Takazudo/zudo-pd/doc/SCAFFOLD.md

# Scaffold provenance

The initializer was run externally into `/tmp/pd-scaffold-S7V5WS/zudo-pd` on 2026-09-29:

```sh
pnpm create zudo-circuit-doc@0.1.0 <empty-scratch>/zudo-pd --name zudo-pd --title zudo-pd --library zudo-pd --agent both --yes --no-git --no-install
```

Each listed path was compared with that output. Exact copies: circuit templates, task examples,
checks README, package island seed and strict link checker. Root manifest/workspace, circuit
workflow/config, AGENTS entry, host manifest/config/routes/styles and ignore rules are merged
or derived; existing site identity, domain, GitHub, logo, CJK, sumi theme, history/body-foot
bindings and #206 header navigation are retained. Existing home route and tsconfig are retained
package-shaped equivalents. Canonical evidence skills were never overwritten.

| Path | Source | Full commit | Date | Track | Sync | Reason |
|---|---|---|---|---|---|---|
| `package.json` | `create-zudo-circuit-doc@0.1.0` output; Takazudo/zudo-circuit-doc scaffold | `5d0e2b630776489d394be341586b889dfe0d1cb8` | 2026-09-29 | releases | rerun pinned initializer externally, diff and merge | Project runtime adoption; preserve host and evidence rules |
| `pnpm-workspace.yaml` | `create-zudo-circuit-doc@0.1.0` output; Takazudo/zudo-circuit-doc scaffold | `5d0e2b630776489d394be341586b889dfe0d1cb8` | 2026-09-29 | releases | rerun pinned initializer externally, diff and merge | Project runtime adoption; preserve host and evidence rules |
| `circuit.config.ts` | `create-zudo-circuit-doc@0.1.0` output; Takazudo/zudo-circuit-doc scaffold | `5d0e2b630776489d394be341586b889dfe0d1cb8` | 2026-09-29 | releases | rerun pinned initializer externally, diff and merge | Project runtime adoption; preserve host and evidence rules |
| `AGENTS.md` | `create-zudo-circuit-doc@0.1.0` output; Takazudo/zudo-circuit-doc scaffold | `5d0e2b630776489d394be341586b889dfe0d1cb8` | 2026-09-29 | releases | rerun pinned initializer externally, diff and merge | Project runtime adoption; preserve host and evidence rules |
| `circuit/WORKFLOW.md` | `create-zudo-circuit-doc@0.1.0` output; Takazudo/zudo-circuit-doc scaffold | `5d0e2b630776489d394be341586b889dfe0d1cb8` | 2026-09-29 | releases | rerun pinned initializer externally, diff and merge | Project runtime adoption; preserve host and evidence rules |
| `circuit/agent-task-examples.md` | `create-zudo-circuit-doc@0.1.0` output; Takazudo/zudo-circuit-doc scaffold | `5d0e2b630776489d394be341586b889dfe0d1cb8` | 2026-09-29 | releases | rerun pinned initializer externally, diff and merge | Project runtime adoption; preserve host and evidence rules |
| `circuit/checks/README.md` | `create-zudo-circuit-doc@0.1.0` output; Takazudo/zudo-circuit-doc scaffold | `5d0e2b630776489d394be341586b889dfe0d1cb8` | 2026-09-29 | releases | rerun pinned initializer externally, diff and merge | Project runtime adoption; preserve host and evidence rules |
| `circuit/templates/**` | `create-zudo-circuit-doc@0.1.0` output; Takazudo/zudo-circuit-doc scaffold | `5d0e2b630776489d394be341586b889dfe0d1cb8` | 2026-09-29 | releases | rerun pinned initializer externally, diff and merge | Project runtime adoption; preserve host and evidence rules |
| `doc/package.json` | `create-zudo-circuit-doc@0.1.0` output; Takazudo/zudo-circuit-doc scaffold | `5d0e2b630776489d394be341586b889dfe0d1cb8` | 2026-09-29 | releases | rerun pinned initializer externally, diff and merge | Project runtime adoption; preserve host and evidence rules |
| `doc/zfb.config.ts` | `create-zudo-circuit-doc@0.1.0` output; Takazudo/zudo-circuit-doc scaffold | `5d0e2b630776489d394be341586b889dfe0d1cb8` | 2026-09-29 | releases | rerun pinned initializer externally, diff and merge | Project runtime adoption; preserve host and evidence rules |
| `doc/tsconfig.json` | `create-zudo-circuit-doc@0.1.0` output; Takazudo/zudo-circuit-doc scaffold | `5d0e2b630776489d394be341586b889dfe0d1cb8` | 2026-09-29 | releases | rerun pinned initializer externally, diff and merge | Project runtime adoption; preserve host and evidence rules |
| `doc/pages/index.tsx` | `create-zudo-circuit-doc@0.1.0` output; Takazudo/zudo-circuit-doc scaffold | `5d0e2b630776489d394be341586b889dfe0d1cb8` | 2026-09-29 | releases | rerun pinned initializer externally, diff and merge | Project runtime adoption; preserve host and evidence rules |
| `doc/pages/docs/[[...slug]].tsx` | `create-zudo-circuit-doc@0.1.0` output; Takazudo/zudo-circuit-doc scaffold | `5d0e2b630776489d394be341586b889dfe0d1cb8` | 2026-09-29 | releases | rerun pinned initializer externally, diff and merge | Project runtime adoption; preserve host and evidence rules |
| `doc/pages/lib/_circuit-doc-islands.ts` | `create-zudo-circuit-doc@0.1.0` output; Takazudo/zudo-circuit-doc scaffold | `5d0e2b630776489d394be341586b889dfe0d1cb8` | 2026-09-29 | releases | rerun pinned initializer externally, diff and merge | Project runtime adoption; preserve host and evidence rules |
| `doc/src/chrome-bindings.tsx` | `create-zudo-circuit-doc@0.1.0` output; Takazudo/zudo-circuit-doc scaffold | `5d0e2b630776489d394be341586b889dfe0d1cb8` | 2026-09-29 | releases | rerun pinned initializer externally, diff and merge | Project runtime adoption; preserve host and evidence rules |
| `doc/src/styles/global.css` | `create-zudo-circuit-doc@0.1.0` output; Takazudo/zudo-circuit-doc scaffold | `5d0e2b630776489d394be341586b889dfe0d1cb8` | 2026-09-29 | releases | rerun pinned initializer externally, diff and merge | Project runtime adoption; preserve host and evidence rules |
| `doc/scripts/check-links.js` | `create-zudo-circuit-doc@0.1.0` output; Takazudo/zudo-circuit-doc scaffold | `5d0e2b630776489d394be341586b889dfe0d1cb8` | 2026-09-29 | releases | rerun pinned initializer externally, diff and merge | Project runtime adoption; preserve host and evidence rules |
| `.gitignore` | `create-zudo-circuit-doc@0.1.0` output; Takazudo/zudo-circuit-doc scaffold | `5d0e2b630776489d394be341586b889dfe0d1cb8` | 2026-09-29 | releases | rerun pinned initializer externally, diff and merge | Project runtime adoption; preserve host and evidence rules |

Underlying create-zudo-doc 5.27.0 host scaffold source:
`zudolab/zudo-doc/packages/create-zudo-doc/templates/default/app`, full commit
`50cbd5c6c9e5a795d72a74a855e105e4939d4eab`. The package docs route retains the explicit
DocHistory binding and now imports the package island seed. Package MDX bindings and CSS
replace project evidence/preview UI; the unrelated task-list CSS workaround remains.

Intentional differences: raw agent resources remain disabled; header navigation is exactly
#206; asset indexing/listing stays off; sitemap is explicitly false because runtime 0.1.0
rejects nonempty sitemaps. TOC toggle, image enlargement and package asset viewer are enabled.
Source link warnings remain active and have a retained project log gate; strict rendered
HTML/anchor checks run in check:site. Public assets retain individual reviewed reasons and
all served paths. Historical PDF attachments do not establish fresh manufacturer verification.

The initializer README's stale “not on npm” paragraph ([upstream #102](https://github.com/Takazudo/zudo-circuit-doc/issues/102)) is deliberately omitted:
initializer/runtime 0.1.0 are published npm packages. Existing project README remains authoritative.
The root lock/workspace is authoritative; both consumers resolve patched runtime 0.1.0.
The global release-age bypass was removed; only observed too-fresh transitive hono@4.13.10
is explicitly excluded (published 2026-09-28T08:20:13Z).

Generated output is semantic parity, not byte identity: view model/report v2, default
zudo-circuit-doc marker, generated notice enabled, package descriptors and zcd classes replace
legacy zld markup. Existing evidence IDs/anchors and claim states remain authoritative.
Exact KiCad renderer digest/version/platform/layers/options remain unchanged; preview bytes
and model bytes remain unchanged. Project browser coverage stays separate: 12 representatives,
1440/375 widths, light/dark, missing-document c335982 and illustrative ASPI provenance. Three
explicit package representatives are supplementary.

Temporary runtime bridge: project #210 and [upstream reports #103–107](../patches/README.md). Keep the committed patch until
released behavior passes the retained compatibility regressions; upstream issue closure alone
is insufficient. No records, candidates, evidence fields or hardware checks were dropped.
The retired `doc/component-docs/` generator, callers and implementation tests are removed by
#208. The committed component pages and their stable history remain under
`doc/src/content/docs/components/`.

## Retained baseline origin

`circuit/tests/runtime-semantic-baseline.json` hashes every record's decoded identity,
aliases, sources, facts, coverage, interactions and pin maps, and all integration rules,
using recursively sorted object keys and preserved array order. It was captured read-only
from the legacy adapter at merged base `88c113ef9acd59e6c6fd6cee099686adf5e1d179` before
legacy retirement. Runtime tests compare the installed package projection to these hashes.
`runtime-anchor-baseline.json` captures every explicit EvidenceAnchor from all 64 committed
legacy pages at that same base. These baselines supplement #205's 313 covered project
file hashes and IDs; they do not assert generated MDX byte identity.

The bridge additionally rejects document exceptions naming nonexistent records, preserving
the old reference contract. The installed package regression is retained in references.test.ts.
At the initial #207 integration, legacy test/caller retirement remained for #208;
193 relocated project assertions, 14 compatibility regressions and the new runtime
contracts exercised the package. Cutover subsequently retained the remaining project
contracts and removed the legacy implementation.

## Asset-viewer publication boundary follow-up

The manager's guarded production build succeeded, but the subsequent real publication
scan rejected `dist/files/component-previews/footprints/manifest.json/index.html`: generic
asset-viewer HTML mirrored a package preview manifest and exposed a denied evidence
`[29].sources[2].sha256` value. The reviewed package manifest hash allowance applies only
to the package-owned artifact; it must not excuse another generated HTML projection.

The host now uses `assetViewerExclude: ["component-previews/**"]`, relative to the
installed zudo-doc 5.27.0 asset directory `public/assets` (verified in its `scanAssets`
and routes-plugin implementation). It excludes footprint SVGs, WRL models and manifests
from generic viewer route generation while retaining their existing public URLs and
package reference cards/inline dialogs. Generic manually authored asset viewing stays
enabled. Asset viewer listing and all indexing are explicitly false. No public assets,
canonical evidence, package patch or scanner/hash checks were changed. A retained
installed-snapshot regression proves an unexcluded manifest becomes viewer HTML, then
proves the host exclusion removes that mirror while a manual asset still renders.

## Browser launcher and heading-extractor bridges

Manager-controlled browser evidence: the unmodified runtime launcher failed the unchanged
idle assertion (`20` → `22`, 45 seconds); the same CLI/site/assertions/timeouts passed all
24 package responsive/theme cases and complete interaction/idle/SPA/fallback/no-JS checks
when a CHROME_BIN wrapper added only the three baseline foreground flags (27 seconds,
minimum memory 6692 MB). The runtime bridge now restores those three flags and the
baseline `Page.bringToFront` lifecycle. Product rendering, idle assertions and timeouts
are unchanged. Upstream: https://github.com/Takazudo/zudo-circuit-doc/issues/108;
removal remains https://github.com/Takazudo/zudo-pd/issues/210. A fake executable/CDP
regression executes the installed launcher and verifies received argv, foreground command
order, normal child/profile cleanup and cleanup on connection failure; it runs no browser.

A separate `@takazudo/zudo-doc@5.27.0` pnpm patch changes only shipped synchronous
`dist/extract-headings/index.js`. Upstream: https://github.com/zudolab/zudo-doc/issues/4428;
independent removal tracker: https://github.com/Takazudo/zudo-pd/issues/211. The strict
scaffold gate found 30 false source-anchor misses after one-line triple-backtick spans in
archived circuit-diagrams, plus four real dead built TOC links where `&gt;1000ms`/`&lt;2mm`
were slugged as literal entity names. The bridge correctly distinguishes inline spans
from true fences and decodes complete Markdown character references exactly once outside
protected escaped/code spans, using the package's declared parse5 full named-entity
parser. Markdown rejects unknown partial names and replaces invalid control/scalar numeric
references; native-pipeline regressions protect those differences from HTML parsing.

`circuit/tests/heading-built-baseline.json` captures all 101 h2–h6 IDs from the manager's
production-built circuit-diagrams, ch224d and linear-regulator-capacitors pages. Additional
fixtures compare installed SDK helpers directly to the pinned zfb 2.21.0 native Markdown
pipeline compiled to WASM, using hierarchical IDs. They cover full named/numeric entities,
escaped/code literals, Unicode arrows/non-Latin, duplicate nesting, h5/h6, true and invalid
fence closers, inline triple spans and indented code. No archived source bytes, evidence,
header navigation, anchor allowlist, strict-check threshold or scanner exceptions changed.

## Long package identity layout bridge

The full 12-representative browser contract found a real c3024223 containment defect at
375px/light: viewer/caption/viewport left 41, right 356.359, width 315.359 exceeded the
reference card's right edge 336 (card width 312). Package label
`SMA_Diodes_SDT5A60SA_C3024223` expanded the viewer's implicit auto-minimum grid track.
Manager-controlled live CSS, with no DOM/text/assertion changes, made all three right edges
319 and widths 278 while preserving the exact label bytes (guard PASS, four seconds,
minimum memory 7507 MB). The proven rule set is now patched into package-owned styles.css:
explicit minmax(0,1fr) viewer column, zero viewer/direct-item minima, caption wrapping and
viewport border-box sizing. No label truncation/clipping and no browser threshold changes.
Upstream: https://github.com/Takazudo/zudo-circuit-doc/issues/109; removal tracker #210.
Long-identity descriptor/SSR/accessible-label and CSS sizing regressions are retained;
the manager reruns all 48 project width/theme cases as the actual geometry proof.
CSS guidance applied: `flexbox-and-grid/grid-patterns.mdx` and
`text-control/long-url-and-path-wrapping.mdx` from zudo-css-wisdom. Identity remains plain
copyable text; no new renderer or host-specific preview stylesheet was introduced.

## Named footprint modal accessibility contract (supersedes the alt bridge)

The earlier migration directive interpreted the project prefix-only enlarged-image alt
assertion as an SDK defect and temporarily restored nonempty image alt under #110.
The combined manager gate then proved that conflicts with the intentional SDK contract:
the media-only modal carries the full accessible description through `aria-label`, while
its enlarged image is decorative (`alt=""`) to avoid a duplicate description. That
inappropriate bridge is removed; the shipped footprint island and first-line client
directive are restored unchanged. #110 is an intentional-design correction, not a runtime
#210 removal prerequisite.

The separate project browser contract now checks the complete semantic identity rather
than the old prefix: inline image alt exactly equals `Footprint preview for <full package
name>`; modal aria-label exactly equals that inline description; enlarged image alt is
empty; no aria-labelledby points at the removed visible title. All other modal, focus,
media containment, load/error, gesture, no-JS, idle assertions and timings are retained.
The installed-island regression exercises the actual trigger, real dialog SSR markup,
exact identity, decorative image and meaningful error fallback with only hooks/modal
effects controlled, without launching a browser. This is the documented package UI
adaptation; no component identity is hidden or truncated. Correction tracking:
https://github.com/Takazudo/zudo-circuit-doc/issues/110.

## Root host lifecycle context

Root build, dev and host checks enter `doc/` through
`circuit/scripts/doc-command.sh`. The wrapper clears the inherited root pnpm
`INIT_CWD` before starting the doc lifecycle, so the history CLI resolves
`src/content/docs` in the actual host. Root PR CI exposed the old context as an
invalid workspace-root history candidate; the strict warning gate remains
unchanged. Explicit local `GEN_DOC_HISTORY=1` verification covers the CI history
path as well as ordinary builds.

Cutover deliberately updates the hash for the live workflow guide
`.claude/skills/component-spec-audit/references/new-component-workflow.md` from
`d47eee9d71c50b15756b1e39236c613027d6ccf285a4aefcd69aa900efbb92b0` to
`73cdc1e7f34e0a3fc72d7260626354b7e2aa74a6c548a521daf4e7a1fd757891`.
The reviewed change describes the actual A/B/P provider and root commands; the
other 312 covered files, canonical evidence, validators and hardware inputs
remain unchanged.

## PR preview first deployment

The PR preview uses the top-level `zudo-pd` Worker; production uses the separate
`production` environment and custom-domain route. Version upload requires an
existing Worker. The CI-only preview helper propagates pipeline failures,
bootstraps the top-level Worker only on Wrangler's specific missing-Worker
error, and requires a returned alias URL before the route smoke can run.
Authentication, bootstrap and retry failures remain failures. All preview calls
explicitly use the empty top-level environment; production commands are unchanged.

References: [Wrangler environments](https://developers.cloudflare.com/workers/wrangler/environments/)
and [aliased version URLs](https://developers.cloudflare.com/workers/versions-and-deployments/version-urls/).
