Takazudo/zudo-pd/notes/diagram.md

## Diagram1: USB-PD給電部

```
USB-C コネクタ                    CH224Q (DFN-10-EP)                LED状態表示回路
┌─────────────┐                ┌──────────────┐                 ┌─────────────┐
│VBUS (B9,A9) ├──┬─────────────┤1. VHV        │                 │   VDD 3.3V  │
│             │  │             │8. VBUS       │─┬─→ 15V出力     │      │      │
│CC1 (A5)     ├──┼─────────────┤7. CC1        │ │               │    330Ω     │
│CC2 (B5)     ├──┼─────────────┤6. CC2        │ │               │   (R1)      │
│GND (B12,A12)├──┼─────────────┤GND           │ │               │      │      │
└─────────────┘  │             │11. EP        │←┘               │   赤色LED   │
                 │             │              │                 │   (LED1)    │
               ┌─C1            │9. CFG1       │←── GND          │      │      │
               │ 10µF/25V      │2. CFG2/SCL   │←── Open         │  PG ────────┘
               │               │3. CFG3/SDA   │←── Open         │              
               └─┬───          │10. PG        │─────────────────┘              
                 │             │4. DP         │    (接続なし)                   
               ┌─C2            │5. DM         │    (接続なし)                   
               │ 10µF/25V      └──────────────┘                                 
               │                      │                                        
               └─┬────────────────────┘                                        
                 │                                                             
                GND
```

## Diagram2: USB-PD給電部 +15V → +13.5V 降圧回路 (LM2596S-ADJ #1)

```
+15V ─────┬─── L1: 100µH ──┬─── D1 ──┬─── C3: 470µF/25V ──┬─→ +13.5V/1.3A
          │    (4.5A)      │   SS34  │    (入力フィルタ)   │
          │                │    ↓    │                    │
          │           ┌────┴─────────┴──┐                 │
          │           │5  VIN      VOUT │4────────────────┤
          └───────────┤3  ON        FB  │2────────┬───────┘
                      │1  GND           │         │
                      └─────────────────┘         │
                              │                   │
                             GND              ┌────┴───┐
                                              │ R1     │ 10kΩ (実際13.53V)
                                              │ 10kΩ   │
                                              └────┬───┘
                                              ┌────┴───┐
                                              │ R2     │ 1kΩ
                                              │ 1kΩ    │
                                              └────┬───┘
                                                   │
                                                  GND
```

## Diagram3: +15V → +7.5V 降圧回路 (LM2596S-ADJ #2)

```
+15V ─────┬─── L2: 100µH ──┬─── D2 ──┬─── C4: 470µF/10V ──┬─→ +7.5V/0.6A
          │    (4.5A)      │   SS34  │    (入力フィルタ)   │
          │                │    ↓    │                    │
          │           ┌────┴─────────┴──┐                 │
          │           │5  VIN      VOUT │4────────────────┤
          └───────────┤3  ON        FB  │2────────┬───────┘
                      │1  GND           │         │
                      └─────────────────┘         │
                              │                   │
                             GND              ┌────┴───┐
                                              │ R3     │ 5.1kΩ (実際7.50V)
                                              │ 5.1kΩ  │
                                              └────┬───┘
                                              ┌────┴───┐
                                              │ R4     │ 1kΩ
                                              │ 1kΩ    │
                                              └────┬───┘
                                                   │
                                                  GND
```

## Diagram4: +15V → -15V 電圧反転回路 (ICL7660)

```
+15V ─────┬─────────────────────────────────────────┬─→ +15V (他回路へ)
          │                                         │
          │           ICL7660M/TR                   │
          │         ┌──────────────┐                │
          └─────────┤2,8  V+   CAP+│1──┐            │
                    │              │   │            │
           GND ─────┤3   GND   CAP-│4──┼─┐          │
                    │              │   │ │          │
          OPEN ─────┤6   LV    V-  │5──┼─┼──────────┴─→ -15V
                    │              │   │ │
          OPEN ─────┤7   OSC       │   │ │
                    └──────────────┘   │ │
                                       │ │
                     C9: 10µF セラミック │ │
                    ┌───────────────────┘ │
                    │                     │
                    └─────────────────────┘
                    
                    C10: 10µF セラミック
                    ┌─────────────────────────┐
                    │                         │
            -15V ───┼─────────────────────────┼─── GND
                    │                         │
                    └─────────────────────────┘
```

**フライングキャパシタ（C9）はPIN1とPIN4の間に直接接続**

```
      フライングキャパシタ C9 (10µF)
           ┌─────────┐
PIN1 ──────┤+       -├────── PIN4
(CAP+)     └─────────┘     (CAP-)
```

## Diagram5: -15V → -13.5V 降圧回路 (LM2596S-ADJ #3)

```
-15V ─────┬─── L3: 100µH ──┬─── D3 ──┬─── C7: 470µF/25V ──┬─→ -13.5V/0.9A
          │    (4.5A)      │   SS34  │    (入力フィルタ)   │
          │                │    ↓    │                    │
          │           ┌────┴─────────┴──┐                 │
          │           │5  VIN      VOUT │4────────────────┤
          └───────────┤3  ON        FB  │2────────┬───────┘
                      │1  GND           │         │
                      └─────────────────┘         │
                              │                   │
                             GND              ┌────┴───┐
                                              │ R5     │ 10kΩ (実際-13.53V)
                                              │ 10kΩ   │
                                              └────┬───┘
                                              ┌────┴───┐
                                              │ R6     │ 1kΩ
                                              │ 1kΩ    │
                                              └────┬───┘
                                                   │
                                                  GND
```

## Diagram6: +13.5V → +12V リニアレギュレータ

```
+13.5V ──┬─── C11: 470nF ───┬─── LM7812 ───┬─── C14: 100nF ───┬─→ +12V/1.2A
         │                  │   (TO-220)   │                  │
         │                  │    ┌─────┐   │                  │
         │                  └────│1 IN │3──┴──────────────────┤
         │                       │     │                      │
         │                    ┌──│2 GND│                      │
         │                    │  └─────┘                      │
         │                    │     │                         │
         └─── C17: 470µF ─────┼─────┼─── C18: 470µF ──────────┤
              (入力安定化)     │     │    (出力安定化)         │
                               │     │                         │
                              GND   GND                       │
                                                              │
                     ┌────────────────────────────────────────┘
                     │
               ┌─────┴─────┐  1kΩ (R7)
               │    LED2   │ ──────┬─→ +12V状態表示 (緑LED)
               │  (緑色)   │       │
               └─────┬─────┘       │
                     │            GND
                    GND
```

## Diagram7: +7.5V → +5V リニアレギュレータ

```
+7.5V ───┬─── C12: 470nF ───┬─── LM7805 ───┬─── C15: 100nF ───┬─→ +5V/1.2A
         │                  │  (TO-220F-3) │                  │
         │                  │    ┌─────┐   │                  │
         │                  └────│1 IN │3──┴──────────────────┤
         │                       │     │                      │
         │                    ┌──│2 GND│                      │
         │                    │  └─────┘                      │
         │                    │     │                         │
         └─── C19: 470µF ─────┼─────┼─── C20: 470µF ──────────┤
              (入力安定化)     │     │    (出力安定化)         │
                               │     │                         │
                              GND   GND                       │
                                                              │
                     ┌────────────────────────────────────────┘
                     │
               ┌─────┴─────┐  1kΩ (R8)
               │    LED3   │ ──────┬─→ +5V状態表示 (青LED)
               │  (青色)   │       │
               └─────┬─────┘       │
                     │            GND
                    GND
```

## Diagram8: -13.5V → -12V リニアレギュレータ

```
-13.5V ──┬─── C13: 470nF ───┬─── LM7912 ───┬─── C16: 100nF ───┬─→ -12V/1.0A
         │                  │   (TO-220)   │                  │
         │                  │    ┌─────┐   │                  │
         │                  └────│1 IN │2──┴──────────────────┤
         │                       │     │                      │
         │                    ┌──│3 GND│                      │
         │                    │  └─────┘                      │
         │                    │     │                         │
         └─── C21: 470µF ─────┼─────┼─── C22: 470µF ──────────┤
              (入力安定化)     │     │    (出力安定化)         │
                               │     │                         │
                              GND   GND                       │
                                                              │
                     ┌────────────────────────────────────────┘
                     │
               ┌─────┴─────┐  1kΩ (R9)
               │    LED4   │ ──────┬─→ -12V状態表示 (赤LED)
               │  (赤色)   │       │
               └─────┬─────┘       │
                     │            GND
                    GND
```

## Diagram9: 保護回路（初心者対応・2段階保護）

```
+12V ──┬─── PTC1: 1.1A ──┬─── F1: 2A ───┬─── TVS1: SMAJ15A ───┬─→ +12V OUT
       │   (自動復帰)     │  (バックアップ)│    (15V一方向)      │
       │                 │              │      ↓              │
       │                 │              └─────GND─────────────┤
       │                 │                                    │
       │                 └─── LED2: 緑 ──[R7: 1kΩ]──┬─→ 電源状態表示
       │                                             │
       │                                            GND
       │
       └─── 段階的保護:
            1. 過負荷 (1.2-2A) → PTC遮断 → 30秒後自動復帰 ✅
            2. 短絡 (>2A) → ヒューズ溶断 → 修理必要 ❌

+5V ───┬─── PTC2: 0.75A ─┬─── F2: 1.5A ──┬─── TVS2: PRTR5V0U2X ─┬─→ +5V OUT
       │   (自動復帰)     │  (バックアップ)│    (5V双方向)        │
       │                 │              │      ↕               │
       │                 │              └─────GND──────────────┤
       │                 │                                    │
       │                 └─── LED3: 青 ──[R8: 1kΩ]──┬─→ 電源状態表示
       │                                             │
       │                                            GND
       │
       └─── 段階的保護 (同上)

-12V ──┬─── PTC3: 0.9A ──┬─── F3: 1.5A ──┬─── TVS3: SMAJ15A ───┬─→ -12V OUT
       │   (自動復帰)     │  (バックアップ)│   (15V一方向逆接続)  │
       │                 │              │      ↑              │
       │                 │              └─────GND─────────────┤
       │                 │                                    │
       │                 └─── LED4: 赤 ──[R9: 1kΩ]──┬─→ 電源状態表示
       │                                             │
       │                                            GND
       │
       └─── 段階的保護 (同上)

※ TVS3は負電圧保護のため、カソードを-12Vライン、アノードをGNDに接続
※ PTCは通常時ほぼ抵抗ゼロ、過電流時に高抵抗化して電流を制限
※ ヒューズはPTCが対応できない急激な短絡から保護
※ LEDが消えたら過負荷 → モジュールを減らして30秒待つ
```

## Diagram10: 電源フロー概要

```
USB-C 15V ──┬─→ +13.5V (DC-DC) ──→ +12V (LDO) ──→ +12V OUT
            │
            ├─→ +7.5V  (DC-DC) ──→ +5V  (LDO) ──→ +5V OUT
            │
            └─→ -15V (反転) ──→ -13.5V (DC-DC) ──→ -12V (LDO) ──→ -12V OUT
```
