Takazudo/zudo-pd/3dp-files/adhesive-leg/generated/four-up.png

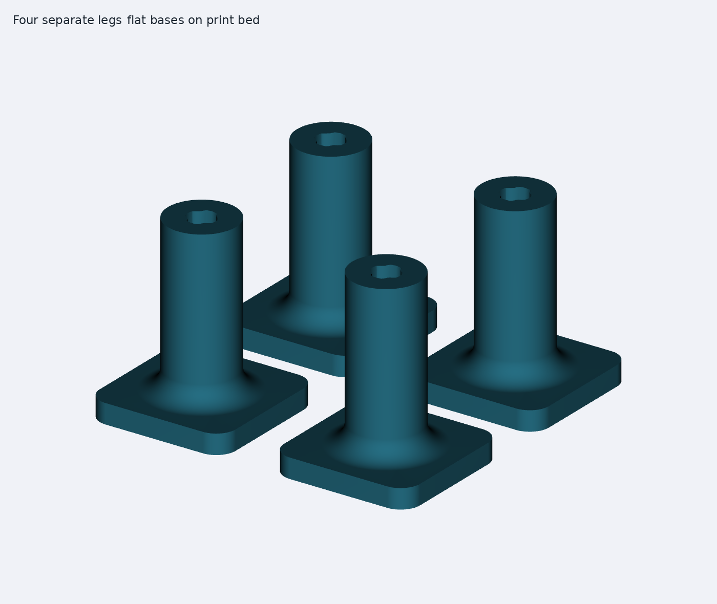
3dp-files/adhesive-leg/generated/four-up.png
