Takazudo/zudo-pd/3dp-files/adhesive-leg/generated/preview.png

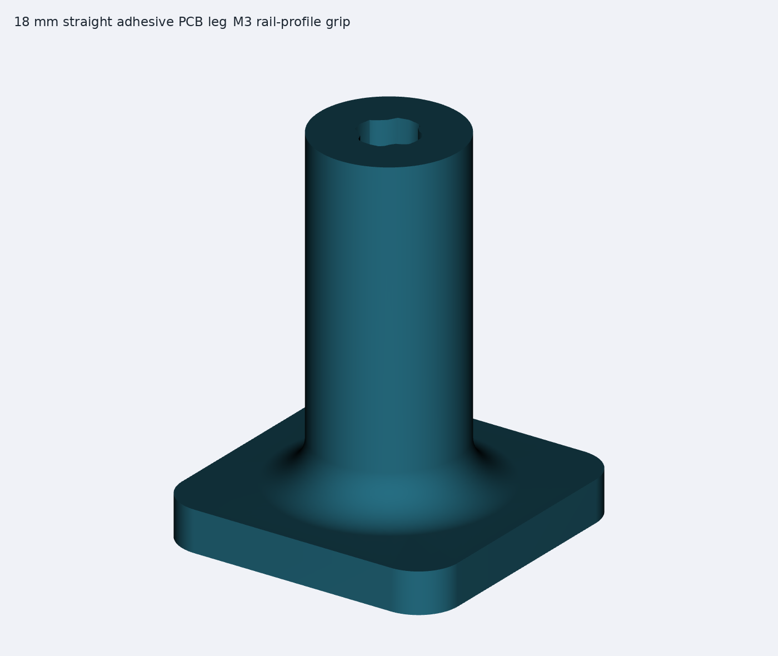
3dp-files/adhesive-leg/generated/preview.png
