Takazudo/zudo-pd/3dp-files/adhesive-leg/generated/section.png

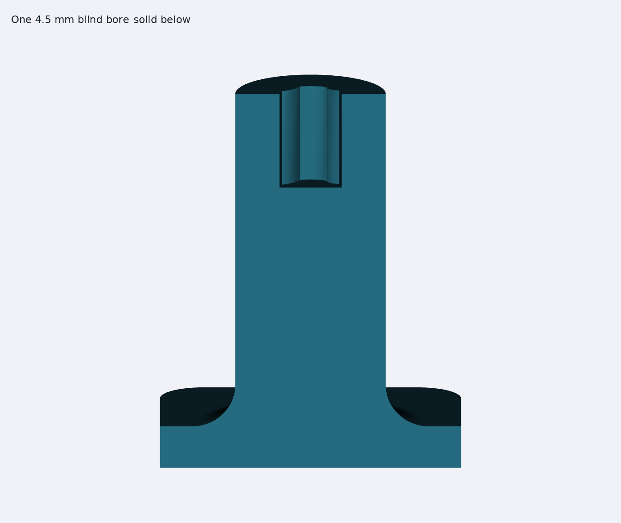
3dp-files/adhesive-leg/generated/section.png
