Takazudo/zudo-pd/boards/board-b/artwork/back-portrait-preview.png

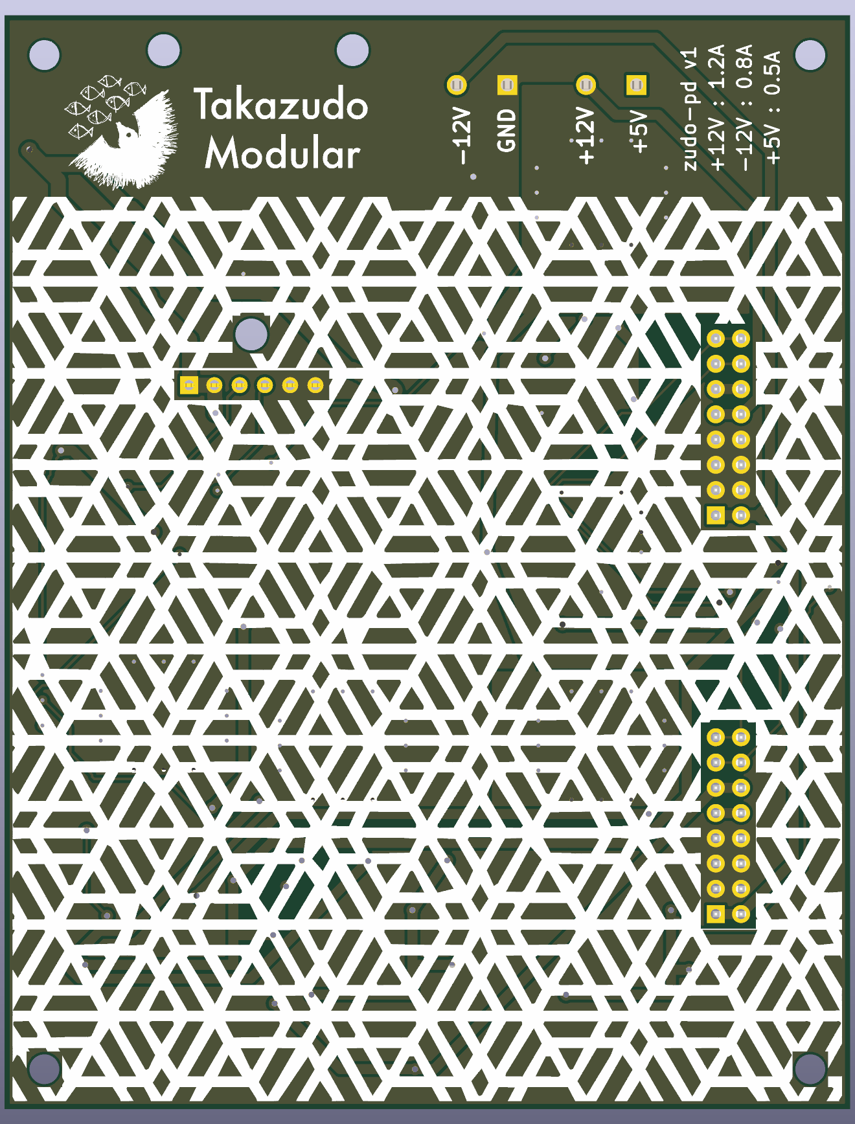
boards/board-b/artwork/back-portrait-preview.png
