Takazudo/zudo-pd/boards/board-b/artwork/back-preview.png

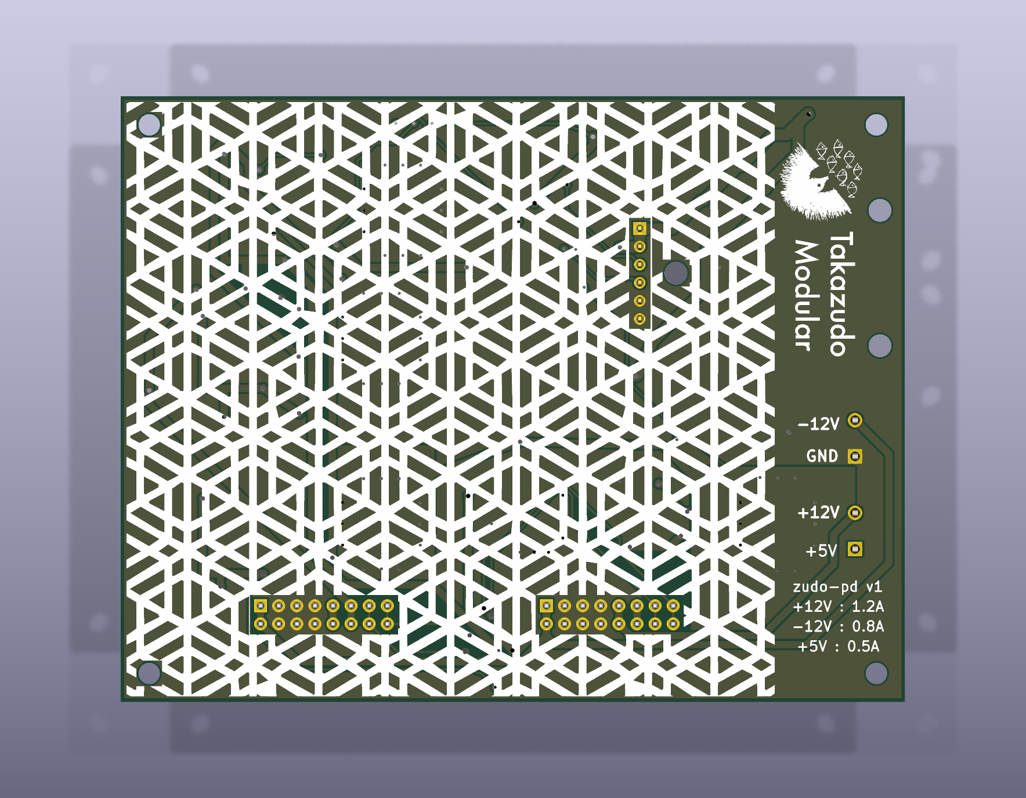
boards/board-b/artwork/back-preview.png
