Takazudo/zudo-pd/doc/src/content/docs/components/l7812cv.md

---
title: L7812CD2T-TR - +12V Linear Regulator
sidebar_position: 9
---

Fixed positive voltage regulator providing stable +12V output in compact TO-263-2 (D2PAK) surface-mount package with excellent thermal performance.

- [View on JLCPCB: C13456](https://jlcpcb.com/partdetail/C13456)
- [Download Datasheet (PDF)](/datasheets/L7812CD2T-datasheet.pdf)

L7812CD2T TO-263-2 Package

## Overview

The L7812CD2T-TR is a three-terminal positive voltage regulator in TO-263-2 (D2PAK) package, designed to provide a fixed +12V output from a higher input voltage. This component serves as the final stage in the +12V power rail, converting the +13.5V DC-DC output to a clean, low-noise +12V suitable for modular synthesizer applications.

## Key Specifications

| Parameter | Value | Notes |
| --- | --- | --- |
| **JLCPCB Part Number** | C13456 | |
| **Manufacturer Part Number** | L7812CD2T-TR | |
| **Package** | TO-263-2 (D2PAK) | Surface-mount |
| **Stock Availability** | 40,204 units | Very high availability |
| **Unit Price** | $0.11 | JLCPCB pricing |
| **Output Voltage** | 12V ±4% | 11.52V - 12.48V |
| **Output Current** | 1.5A max | Design uses 1.2A |
| **Dropout Voltage** | ~2V typical | Minimum VIN = 14V |
| **Line Regulation** | ±0.5% typical | Input voltage variation  |
| **Load Regulation** | ±1% typical | Output current variation |
| **Ripple Rejection** | &gt;60dB | @120Hz |
| **Quiescent Current** | ~5mA typical | No-load consumption |
| **Thermal Resistance θJC** | 3°C/W | Junction to case (tab) |
| **Thermal Resistance θJA** | 35°C/W | Junction to ambient |
| **Operating Temp Range** | 0°C to +125°C | Junction temperature |

## Pin Configuration

```
         TO-263-2 (D2PAK) Package
              Top View

         ┌──────────────┐
         │              │
         │   L7812C     │
         │   D2T-TR     │
         │              │
         │              │
         └──┬───────┬───┘
            │       │
          PIN1    PIN2
          INPUT    GND
         (+13.5V) (Common)

              TAB
           (OUTPUT)
            (+12V)

         Side View

         ┌──────────────┐
         │   Component  │ ← Surface mount IC
         └──┬───────┬───┘
            │       │
          PIN1    PIN2

    ════════════════════  ← Metal tab (OUTPUT)
                            soldered to PCB pad
```

### Pin Descriptions

| Pin | Name | Function | Connection in Design |
| --- | --- | --- | --- |
| 1 | INPUT  | Unregulated input voltage | +13.5V from DC-DC converter (U2)  |
| 2 | GND | Ground reference (common) | System ground plane |
| TAB | OUTPUT | Regulated +12V output (metal tab) | +12V rail with protection circuit |

**Note**: Unlike TO-220 package, the TO-263-2 has the OUTPUT on the metal tab, not on pin 3.

## Application Circuit

```
+13.5V (from DC-DC) ───┬─── C11: 470nF ───┬─── U6: L7812CD2T ───┬─── C14: 100nF ───┬─→ +12V OUT
                       │                  │                      │                  │
                       │                  │    ┌──────────┐      │                  │
                       │                  └────│1  INPUT  │      │                  │
                       │                       │          │      │                  │
                       │                    ┌──│2   GND   │      │                  │
                       │                    │  │          │      │                  │
                       │                    │  │   TAB ───┴──────┴──────────────────┤
                       │                    │  └──────────┘                         │
                       │                    │     (OUTPUT)                          │
                       └─── C17: 470µF ─────┼─────────┬─── C18: 470µF ──────────────┤
                            (Input)         │         │    (Output)                 │
                                            │         │                             │
                                           GND       GND                            │
                                                                                    │
                                        ┌───────────────────────────────────────────┘
                                        │
                                  ┌─────┴─────┐
                                  │   LED2    │ Green Status LED
                                  │  (Green)  │ via R7: 1kΩ
                                  └─────┬─────┘
                                        │
                                       GND
```

## Component Values

### Input Capacitors

| Reference | Value | Type | Voltage | Package | Part Number | Purpose |
| --- | ----- | --- | --- | --- | --- | --- |
| C11 | 470nF | Ceramic X7R  | 25V | 0603 | C1623 | High-frequency noise filtering |
| C17 | 470µF | Electrolytic | 10V | D6.3xL7.7mm | C335982 | Input voltage stabilization |

### Output Capacitors

| Reference | Value | Type | Voltage | Package | Part Number | Purpose |
| --- | ----- | --- | --- | --- | --- | --- |
| C14 | 100nF | Ceramic X7R  | 50V | 0805 | C1711 | High-frequency decoupling |
| C18 | 470µF | Electrolytic | 10V | D6.3xL7.7mm | C335982 | Load transient response |

### Status LED Circuit

| Reference | Part | Value | Package | Part Number | Purpose |
| --- | --- | --- | --- | --- | --- |
| LED2 | Green LED | 2.0V @ 10mA | 0805 | C72043 | Power status indicator |
| R7 | Resistor  | 1kΩ | 0603 | C21190 | LED current limiting |

## Design Considerations

### Input Voltage Requirements

The L7812CV requires a minimum input voltage of approximately 14V for proper regulation (12V output + 2V dropout). In this design:

- **Input voltage**: +13.5V from LM2596S DC-DC converter
- **Dropout margin**: 13.5V - 12V = 1.5V
- **Status**: ⚠️ Marginal - operates near minimum dropout voltage

The 1.5V margin is slightly below the typical 2V dropout specification but acceptable because:

1. The DC-DC stage is regulated at 13.5V (not 13.53V as calculated from feedback)
2. The L7812CV can regulate with 1.5V dropout at lower currents
3. Actual load current (1.2A) is below maximum rating (1.5A)

**Recommendation**: For production, consider increasing DC-DC output to 14.0V for better dropout margin.

### Thermal Management

Power dissipation calculation:

```
P = (VIN - VOUT) × IOUT
P = (13.5V - 12V) × 1.2A
P = 1.5V × 1.2A
P = 1.8W
```

Temperature rise without additional heatsinking:

```
ΔT = P × θJA
ΔT = 1.8W × 35°C/W
ΔT = 63°C
```

At 25°C ambient, junction temperature = 88°C (well within 125°C maximum).

**Thermal performance advantages of TO-263-2**:

- Lower θJA than TO-220 (35°C/W vs 50°C/W)
- Large metal tab provides excellent heat spreading
- Direct thermal contact with PCB copper pour
- No additional heatsink required for this application

**PCB copper area recommendations**:

- Minimum: 3 cm² copper pour connected to tab
- Recommended: 6 cm² copper pour for better margin
- Thermal vias: 6-10 vias (0.3mm) under tab to bottom layer

### Capacitor Placement

Critical for stability and noise rejection:

1. **C11 (470nF ceramic)**: Place within 5mm of pin 1

- Purpose: Suppress high-frequency noise from DC-DC stage
- Type: X7R or better (C0G ideal but more expensive)

2. **C17 (470µF electrolytic)**: Place within 10mm of pin 1

- Purpose: Stabilize input voltage during load transients
- Polarity: Positive terminal to input, negative to ground

3. **C14 (100nF ceramic)**: Place within 5mm of output tab

- Purpose: High-frequency output decoupling
- Critical for preventing oscillation
- Must be ceramic for low ESR/ESL

4. **C18 (470µF electrolytic)**: Place within 10mm of output tab

- Purpose: Improve load transient response
- ESR: &lt;2Ω for best performance
- Helps with sudden current demands

### Ground Plane Connection

The TO-263-2 package requires careful PCB layout:

- **Pin 2 (GND)**: Connect directly to ground plane with wide trace
- **Tab (OUTPUT)**: Large copper pour for both electrical and thermal connection
- **Thermal vias**: Essential for heat dissipation to inner/bottom layers
- **Keep-out area**: Maintain clearance around pins for solder inspection

## Performance Characteristics

### Regulation Performance

| Condition | Specification | Typical Performance |
| --- | --- | --- |
| Line regulation | VIN = 14.5V to 27V | ±0.5% (±60mV) |
| Load regulation | IOUT = 5mA to 1.5A | ±1% (±120mV) |
| Output voltage accuracy | At 25°C | ±4% (±480mV) |
| Temperature coefficient | -40°C to +125°C | ±1mV/°C typical |

### Noise Performance

| Parameter | Value | Conditions |
| --- | --- | --- |
| Ripple rejection | 60dB min | f = 120Hz |
| Output noise voltage | &lt;1mVp-p | With recommended capacitors |
| Transient response | &lt;50µs | 500mA load step |

## Protection Features

### Built-in Protections

1. **Thermal Shutdown**: Automatically shuts down if junction temperature exceeds 150°C
2. **Short Circuit Protection**: Current limiting prevents damage during output short
3. **Safe Operating Area (SOA)**: Internal circuitry ensures operation within safe limits

### External Protection (This Design)

```
+12V (from U6) ──┬─── PTC1: 1.1A ──┬─── F1: 2A ───┬─── TVS1: SMAJ15A ───┬─→ +12V OUT
                 │  (Auto-Reset)   │   (Backup)   │   (15V Clamp)       │
                 │                 │              │      ↓              │
                 │                 │              └─────GND─────────────┤
                 │                 │                                    │
                 └─── LED2 (Green) via R7 (1kΩ) ──────────────→ Power Status
```

Protection stages:

1. **Overload (1.2A-2A)**: PTC1 trips → Auto-reset after cooling
2. **Short circuit (&gt;2A)**: F1 blows → Manual replacement required
3. **Overvoltage**: TVS1 clamps transients above 15V

## Bill of Materials

| Designator | Part | Value | Package | JLCPCB Part # | Qty | Unit Price | Extended  |
| --- | --- | --- | --- | --- | --- | --- | --- |
| U6 | L7812CD2T-TR | Fixed +12V LDO | TO-263-2 | C13456 | 1 | $0.11 | $0.11 |
| C11 | Ceramic Cap  | 470nF 25V X7R  | 0603 | C1623 | 1 | $0.0036 | $0.0036 |
| C14 | Ceramic Cap  | 100nF 50V X7R  | 0805 | C1711 | 1 | $0.0021 | $0.0021 |
| C17, C18 | Electrolytic | 470µF 10V | D6.3xL7.7mm | C335982 | 2 | $0.014 | $0.028 |
| LED2 | LED | Green 0805 | 0805 | C72043 | 1 | $0.0126 | $0.0126 |
| R7 | Resistor | 1kΩ ±1% | 0603 | C21190 | 1 | $0.0005 | $0.0005 |
| | | | | **Total** | | | **$0.16** |

## Alternative Parts

### Direct Replacements (TO-263-2 Package)

| Part Number | Manufacturer | JLCPCB Part # | Stock  | Price  | Notes |
| --- | --- | --- | --- | --- | --- |
| L7812CD2T-TR  | STMicroelectronics | C13456 | 40,204 | $0.11  | Recommended (very high stock) |
| L7812ABD2T-TR | STMicroelectronics | C186698 | 2,056  | $0.11  | Pin-compatible |
| MC7812BDTRKG  | ON Semiconductor | C126398 | 3,549  | ~$0.12 | Pin-compatible (TO-252-2) |

### Package Alternatives

| Package  | Part Number  | JLCPCB Part # | Stock | Price | Notes |
| --- | --- | --- | --- | ----- | --- |
| TO-263-2 | L7812CD2T-TR | C13456 | 40,204  | $0.11 | **Recommended** (best thermal) |
| TO-220 | L7812CV-DG | C2914 | 158,795 | $0.11 | Through-hole alternative |
| TO-252-2 | CJ7812 | C26184 | 9,985 | $0.11 | SMD alternative |

**Recommendation**: Stick with TO-263-2 for SMD assembly and superior thermal performance.

## PCB Layout Guidelines

### Footprint Requirements

TO-263-2 (D2PAK) package footprint specifications:

```
         Top View (PCB Pad Layout)

    ┌──────────────────────────────┐
    │                              │
    │    Large Copper Pour         │  ← OUTPUT TAB
    │    (6cm² recommended)        │     thermal + electrical
    │                              │
    │         Thermal Vias         │
    │         (6-10 vias)          │
    │                              │
    └──────────────────────────────┘

         PIN1 ■        PIN2 ■
        (INPUT)        (GND)

    Pin spacing: 2.54mm (0.1")
    Pin pad: 1.5mm x 2.0mm
    Tab pad: 10mm x 10mm (minimum)
            15mm x 15mm (recommended)
```

### Recommended Pad Dimensions

| Pad | Width | Length  | Purpose |
| --- | --- | --- | --- |
| Pin 1 (INPUT) | 1.5mm | 2.0mm | Solder pad for input pin |
| Pin 2 (GND) | 2.0mm | 3.0mm | Larger for ground connection |
| Tab (OUTPUT)  | 10-15mm | 10-15mm | Thermal and electrical connection |

### Layout Recommendations

1. **Component placement**:

- Orient IC with tab facing interior of PCB (away from edge)
- Maximize copper area under and around tab
- Keep input and output capacitors on same side as regulator

2. **Copper pours**:

- Create large copper pour (6cm² minimum) connected to output tab
- Top layer: Main output pad and distribution
- Bottom layer: Additional copper connected via thermal vias
- Inner layers (4-layer board): Additional ground/power planes

3. **Thermal vias**:

- Place 6-10 thermal vias (0.3mm diameter) under tab
- Arrange in grid pattern for even heat distribution
- Connect to bottom layer copper pour
- Do NOT use thermal relief on these vias (direct connection needed)
- Via spacing: ~2mm apart

4. **Trace widths**:

- Input trace (13.5V): 1mm minimum (1.2A current)
- Output trace (12V): 1mm minimum (1.2A current)
- Ground: Maximum copper pour area
- High-current paths: 2mm or copper pour preferred

5. **Capacitor placement**:

   ```
   C11 ──┐  ┌── IC ──┐  ┌── C14
         │  │        │  │
   C17 ──┘  │  U6    │  └── C18
            │        │
            └────────┘

   Distance:
   - C11: <5mm from pin 1
   - C17: <10mm from pin 1
   - C14: <5mm from output tab
   - C18: <10mm from output tab
   ```

## Testing and Validation

### Input Voltage Test

1. Apply 13.5V to input with no load
2. Verify output voltage: 11.52V - 12.48V (12V ±4%)
3. Measure quiescent current: &lt;10mA

### Load Regulation Test

1. Connect variable load (0-1.5A)
2. Measure output voltage at different load currents:

- 0mA: Should be within 12V ±2%
- 500mA: Should be within 12V ±3%
- 1200mA: Should be within 12V ±4%

3. Verify voltage drop &lt;120mV from no-load to full-load

### Thermal Test

1. Apply 1.2A load for 30 minutes
2. Measure case temperature with thermal camera or thermocouple
3. Verify case temperature &lt;100°C at 25°C ambient
4. Check for thermal shutdown (should not occur)

### Ripple and Noise Test

1. Connect oscilloscope (AC coupling, 20MHz bandwidth)
2. Measure output with 1.2A load
3. Verify peak-to-peak ripple &lt;5mVp-p (target: &lt;1mVp-p)
4. Check for oscillation or instability

## Troubleshooting

| Symptom | Possible Cause | Solution |
| --- | --- | --- |
| No output voltage  | Input voltage too low | Verify 13.5V input |
| | Shorted output | Check for shorts on +12V rail |
| | Thermal shutdown | Reduce load or improve cooling |
| Low output voltage | Insufficient input voltage  | Check DC-DC stage output |
| | Excessive load current | Verify load &lt;1.2A |
| | Poor ground connection | Check pin 2 connection |
| High ripple noise  | Missing input capacitor | Verify C11, C17 installed |
| | Missing output capacitor | Verify C14, C18 installed |
| | Poor capacitor placement | Move capacitors closer to IC |
| Oscillation | Missing output capacitor | Add C14 (100nF) |
| | Long output traces | Shorten traces, add decoupling |
| | Inductive output load | Add output capacitor closer to load |
| Overheating | Excessive power dissipation | Reduce load current |
| | No heatsink | Add heatsink or improve PCB cooling |
| | Poor thermal contact | Check mounting and thermal vias |

## Related Components

- **Upstream**: LM2596S-ADJ #1 (U2) - Provides +13.5V input
- **Downstream**: Protection circuit (PTC1, F1, TVS1)
- **Parallel regulators**: L7805ABD2T-TR (U7), CJ7912 (U8)

## References

- [L7812CV Datasheet](https://www.st.com/resource/en/datasheet/l78.pdf) - STMicroelectronics
- [JLCPCB Part C2914](https://jlcpcb.com/partdetail/C2914)
- [Linear Regulator Design Guide](https://www.st.com/resource/en/application_note/an2202.pdf)
- Related documentation: [Diagram5 - +12V Linear Regulator](../overview/circuit-diagrams.mdx#diagram5-135v--12v-linear-regulator-l7812-u6)
