Takazudo/zudo-pd/3dp-files/adhesive-leg/generated/installed.png

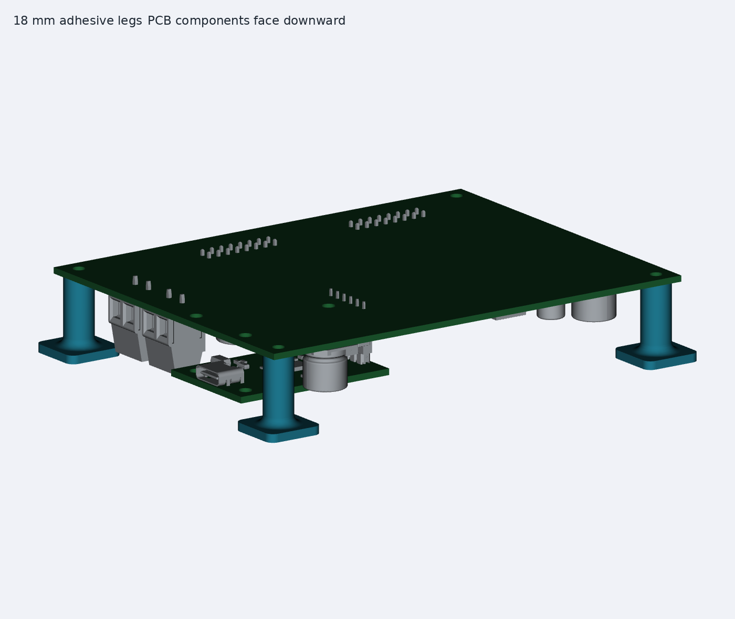
3dp-files/adhesive-leg/generated/installed.png
