Takazudo/zudo-pd/boards/board-b/assembly-preview/top.png

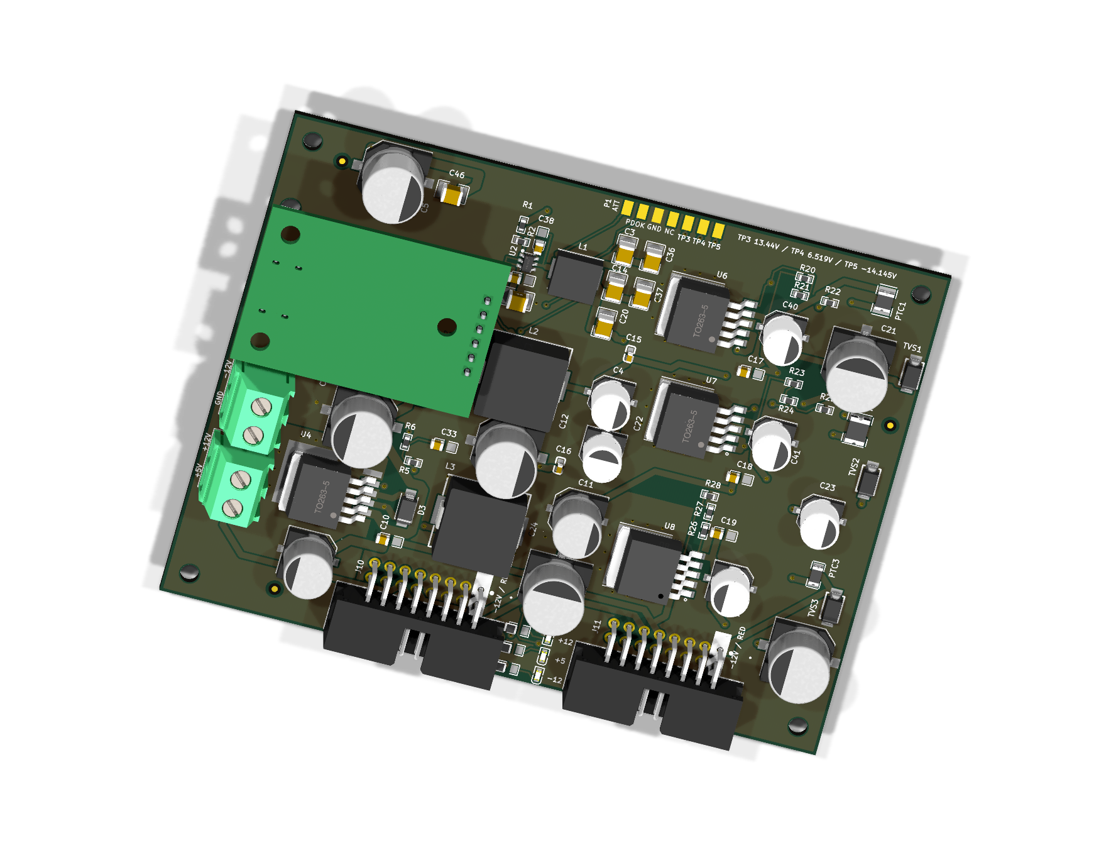
boards/board-b/assembly-preview/top.png
