Takazudo/zudo-pd/manufacturing/releases/corner-support-review/board-b/gerber-bottom.png

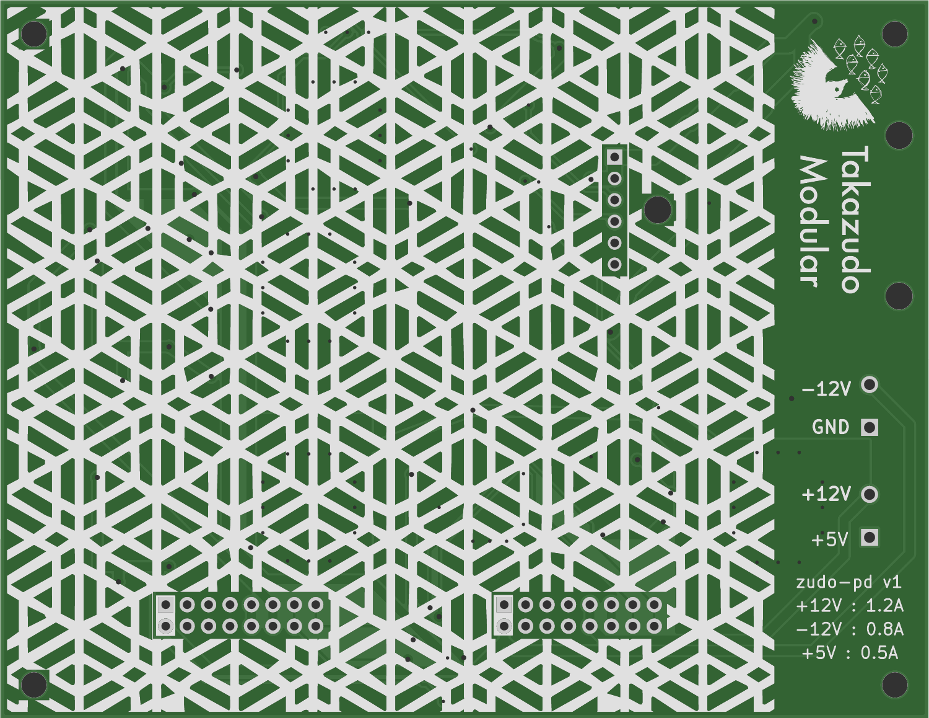
manufacturing/releases/corner-support-review/board-b/gerber-bottom.png
