Takazudo/zudo-pd/manufacturing/releases/corner-support-review/board-b/gerber-top.png

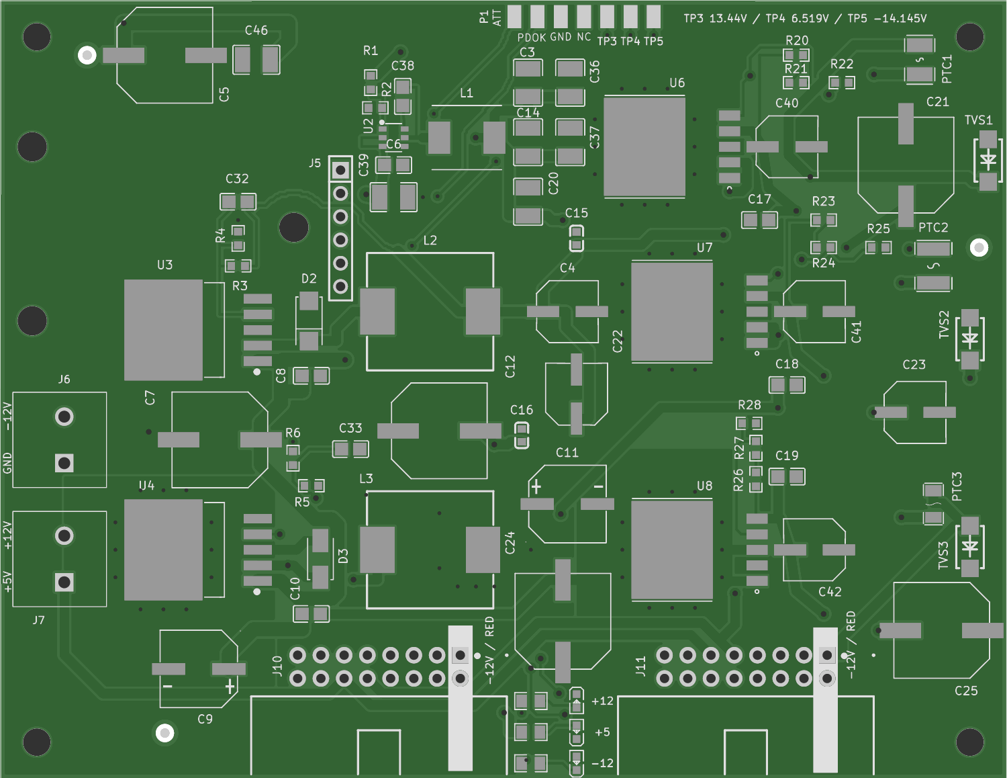
manufacturing/releases/corner-support-review/board-b/gerber-top.png
