Takazudo/zudo-pd/manufacturing/releases/corner-support-review/board-p/3d-top.png

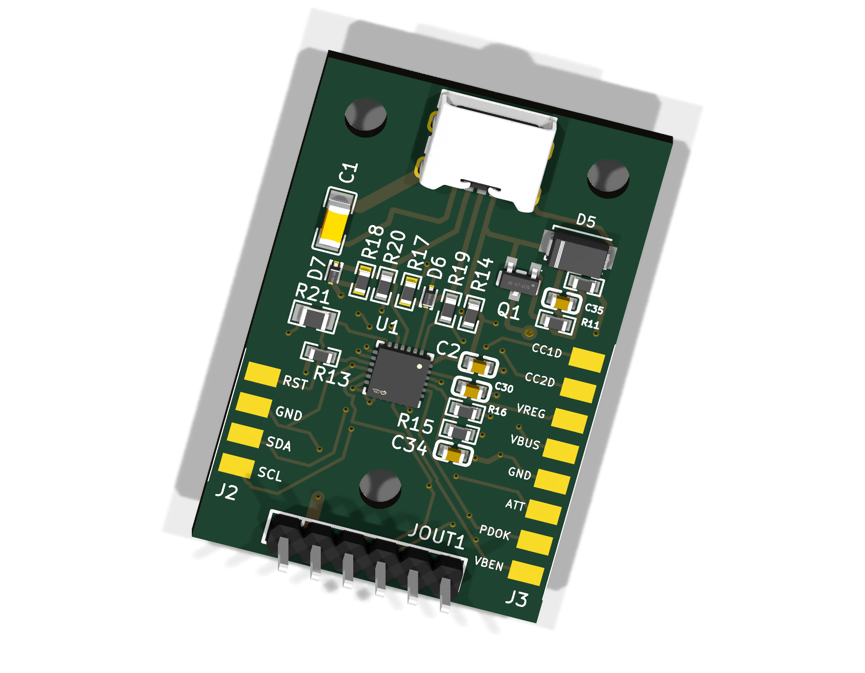
manufacturing/releases/corner-support-review/board-p/3d-top.png
