Takazudo/zudo-pd/manufacturing/releases/corner-support-review/board-p/gerber-bottom.png

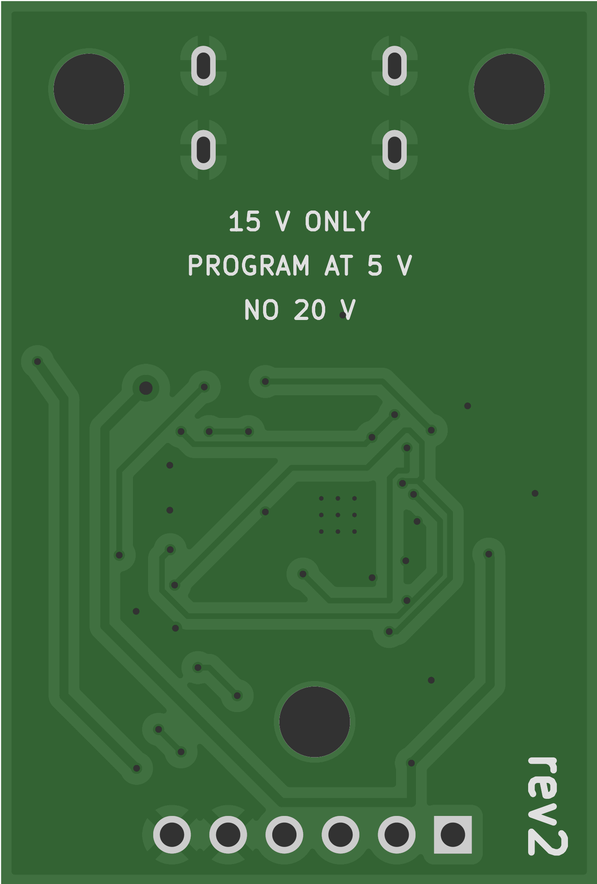
manufacturing/releases/corner-support-review/board-p/gerber-bottom.png
